jonnyfishman/Keiser-BLE-Power-Meter/BLE_Power/PowerData.c

#include "PowerData.h"
#include <avr/pgmspace.h>

const unsigned int GEAR8[] PROGMEM = {
    0,0,0,0,0,0,0,0,0,0,0,0,0,0,0,1,1,2,2,3,4,4,5,6,6,7,8,8,9,10,11,11,12,13,14,15,15,16,17,18,18,19,20,21,22,22,23,24,25,26,26,27,28,29,30,30,31,32,33,34,35,35,36,37,38,39,40,41,42,43,44,44,45,46,47,48,49,50,51,52,53,54,55,56,57,58,59,60,61,62,63,64,65,66,67,68,69,70,71,72,73,74,75,76,77,78,79,80,81,81,82,83,84,85,86,87,88,89,90,91,92,93,94,95,96,97,98,100,101,102,103,105,106,107,109,111,112,114,116,118,120
};
const unsigned int GEAR9[] PROGMEM = {
    0,0,0,0,0,0,0,0,0,0,0,0,1,1,2,2,3,4,4,5,6,6,7,8,9,10,10,11,12,13,14,15,15,16,17,18,19,20,21,22,23,24,24,25,26,27,28,29,30,31,32,33,34,35,36,37,38,39,40,41,42,43,44,46,47,48,49,50,51,52,53,55,56,57,58,59,61,62,63,64,66,67,68,69,71,72,73,74,76,77,78,80,81,82,83,85,86,87,89,90,91,93,94,95,96,98,99,100,101,103,104,105,107,108,109,110,112,113,114,116,117,119,120,121,123,124,126,128,129,131,133,134,136,138,140,143,145,147,150,152,155
};
const unsigned int GEAR10[] PROGMEM = {
    0,0,0,0,0,0,0,0,0,0,0,0,0,1,1,2,3,3,4,5,6,7,8,9,10,11,12,13,14,15,16,17,18,19,20,21,22,23,24,25,27,28,29,30,31,32,33,35,36,37,38,39,41,42,43,44,45,47,48,49,50,52,53,54,56,57,58,60,61,62,64,65,67,68,70,71,72,74,75,77,78,80,81,83,84,86,87,89,90,92,93,95,96,98,99,101,102,104,105,107,108,110,111,113,114,115,117,118,120,121,123,124,126,127,129,130,132,133,135,136,138,139,141,142,144,146,148,150,151,153,155,158,160,162,165,167,170,173,175,179,182
};
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
};
